bmiddha/shin-ramyun-ai/3D/new_flap.SLDPRT

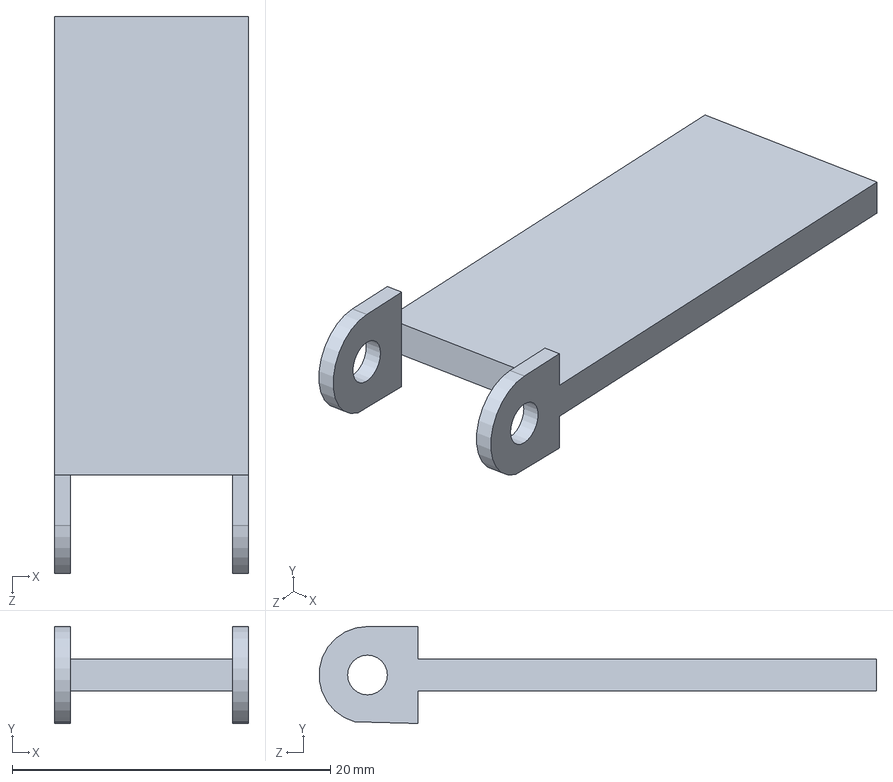
[picture p40: CAD file, 2019-05-07]
3D/new_flap.SLDPRT
12.2 x 6.10 x 35.0 mm
