bmiddha/shin-ramyun-ai/3D/Column Section.SLDPRT

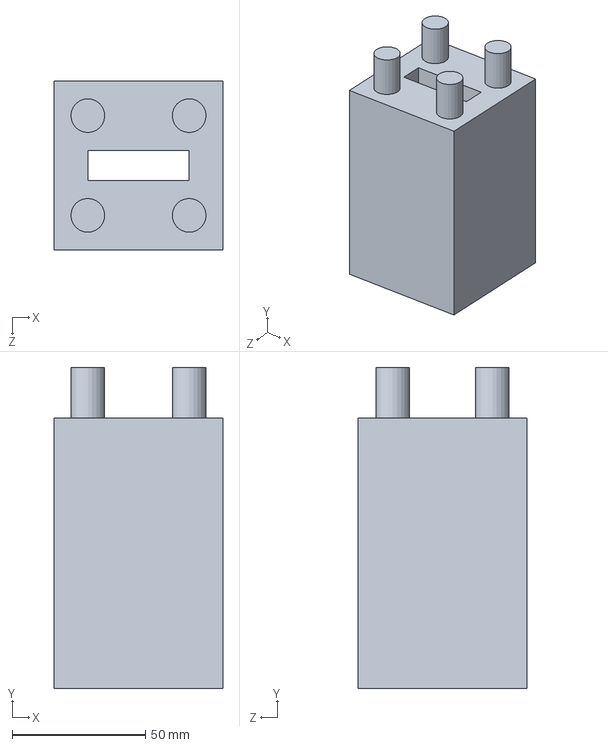
[picture p41: CAD file, 2019-05-07]
3D/Column Section.SLDPRT
63.5 x 120.7 x 63.5 mm
