bmiddha/shin-ramyun-ai/3D/HopperBottom.SLDPRT

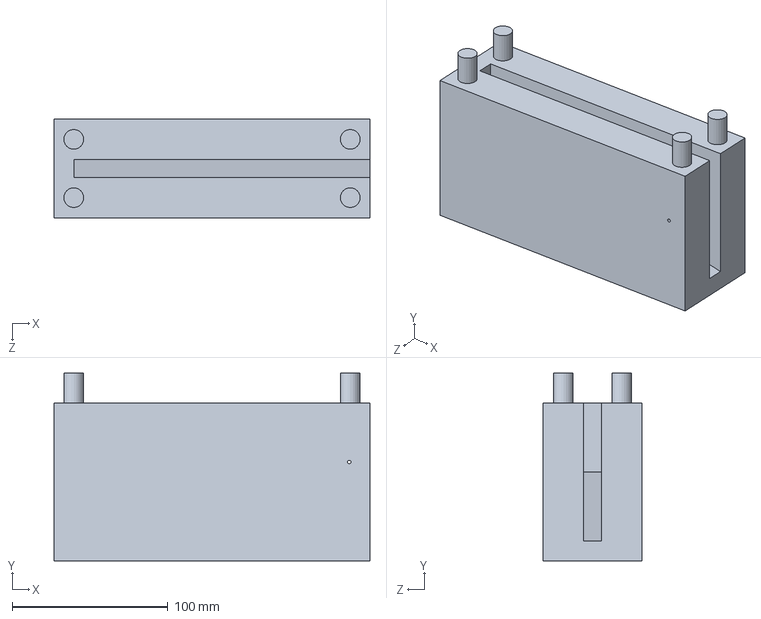
[picture p42: CAD file, 2019-05-07]
3D/HopperBottom.SLDPRT
203.2 x 120.7 x 63.5 mm
