bmiddha/shin-ramyun-ai/3D/Flap_Holder_left.SLDPRT

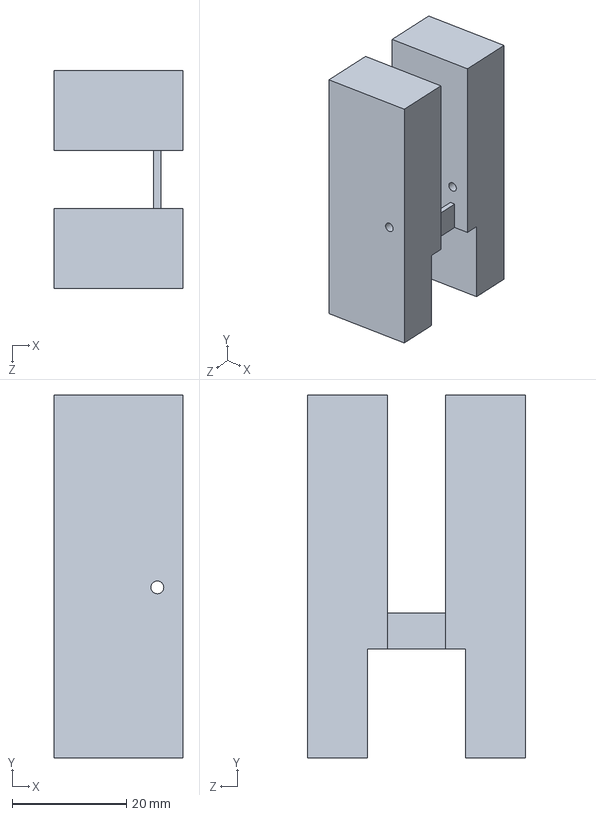
[picture p43: CAD file, 2019-05-07]
3D/Flap_Holder_left.SLDPRT
22.5 x 63.5 x 38.1 mm
