bmiddha/shin-ramyun-ai/3D/column_side.DXF

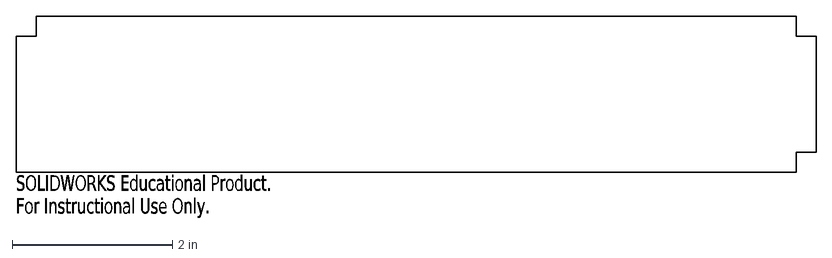
[picture p44: CAD file, 2019-05-07]
3D/column_side.DXF
SOLIDWORKS Educational Product.
For Instructional Use Only.
