bmiddha/shin-ramyun-ai/3D/DispenserRotor.SLDPRT

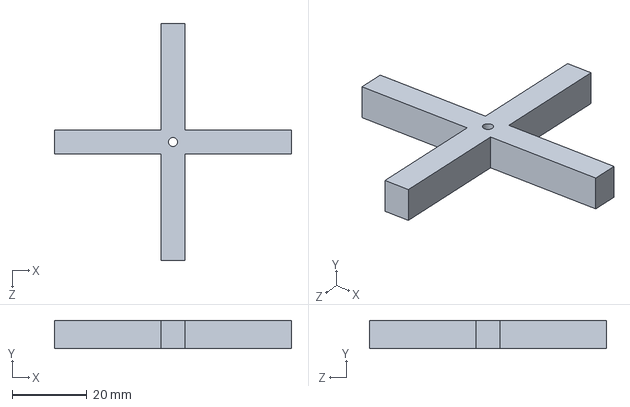
[picture p45: CAD file, 2019-05-07]
3D/DispenserRotor.SLDPRT
63.5 x 7.62 x 63.5 mm
