bmiddha/shin-ramyun-ai/3D/Connect4_Piece.SLDPRT

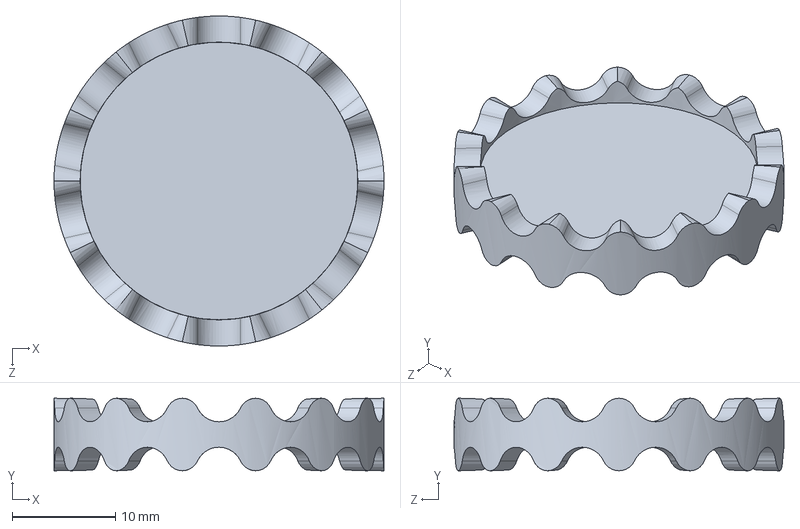
[picture p46: CAD file, 2019-05-07]
3D/Connect4_Piece.SLDPRT
32.0 x 7.04 x 32.0 mm
