bmiddha/shin-ramyun-ai/3D/Flap_Holder.SLDPRT

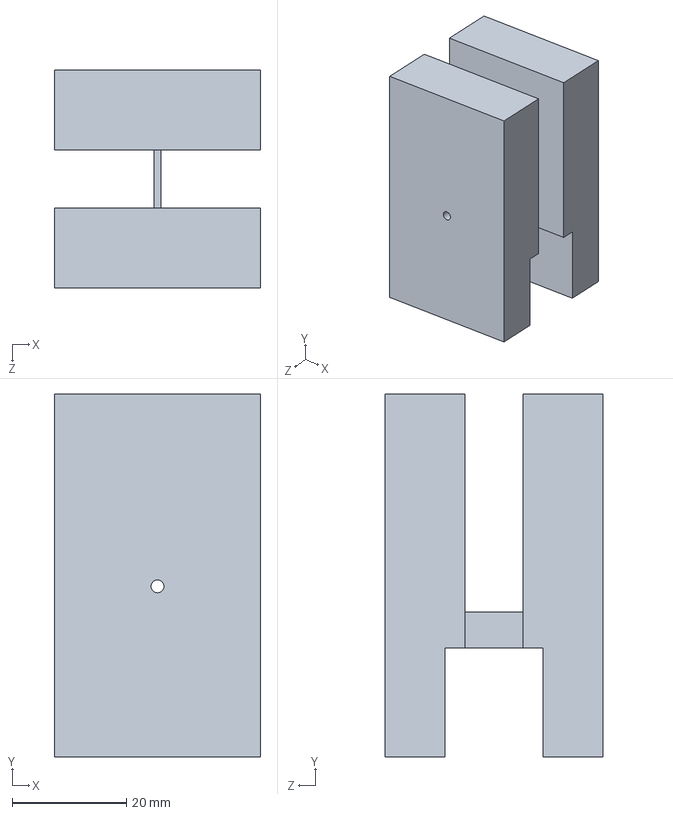
[picture p47: CAD file, 2019-05-07]
3D/Flap_Holder.SLDPRT
36.1 x 63.5 x 38.1 mm
