bmiddha/shin-ramyun-ai/3D/short_i.DXF

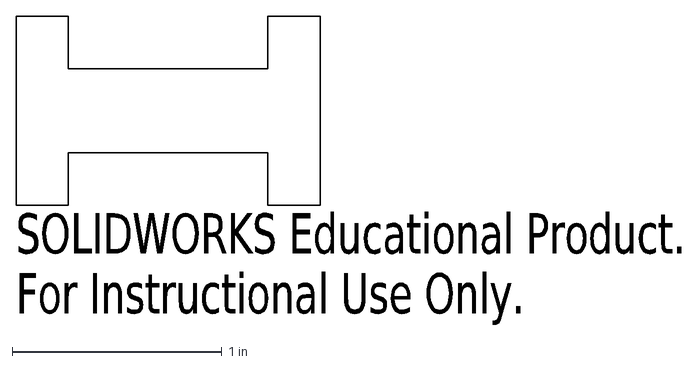
[picture p48: CAD file, 2019-05-07]
3D/short_i.DXF
SOLIDWORKS Educational Product.
For Instructional Use Only.
