bmiddha/shin-ramyun-ai/3D/motor_mount_long.SLDPRT

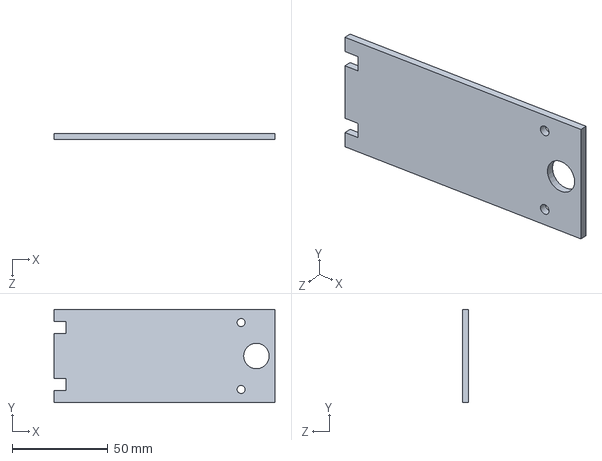
[picture p49: CAD file, 2019-05-07]
3D/motor_mount_long.SLDPRT
115.6 x 48.8 x 3.17 mm
