bmiddha/shin-ramyun-ai/3D/extender_plate.SLDPRT

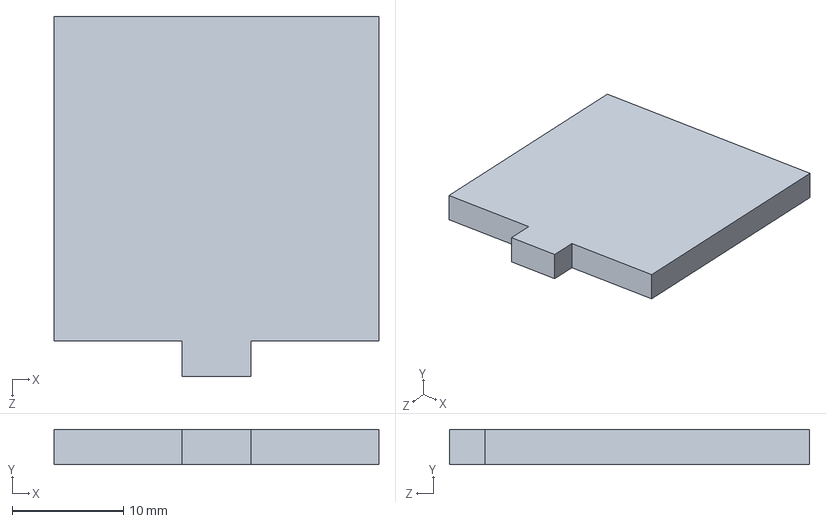
[picture p50: CAD file, 2019-05-07]
3D/extender_plate.SLDPRT
29.2 x 3.17 x 32.4 mm
