bmiddha/shin-ramyun-ai/3D/Connect4_board.SLDPRT

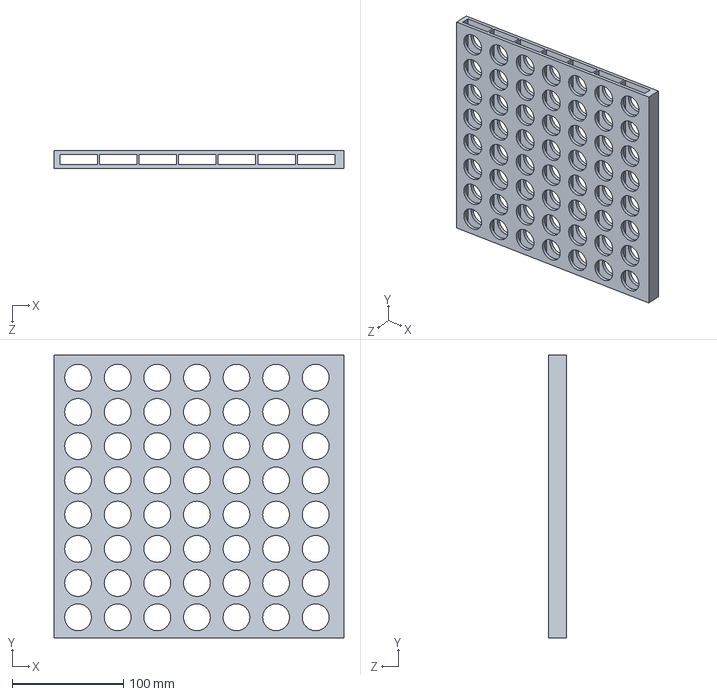
[picture p51: CAD file, 2019-05-07]
3D/Connect4_board.SLDPRT
260.3 x 254.0 x 16.5 mm
