bmiddha/shin-ramyun-ai/3D/2mm_axle.SLDPRT

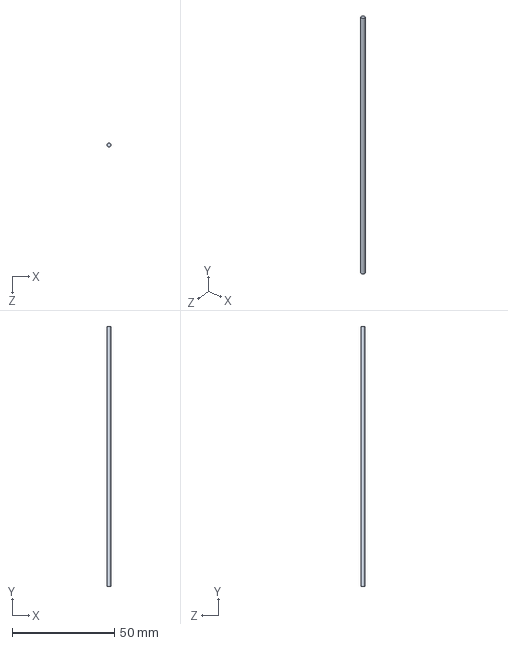
[picture p52: CAD file, 2019-05-07]
3D/2mm_axle.SLDPRT
2.00 x 127.0 x 2.00 mm
