bmiddha/shin-ramyun-ai/3D/Flap_Holder_end.SLDPRT

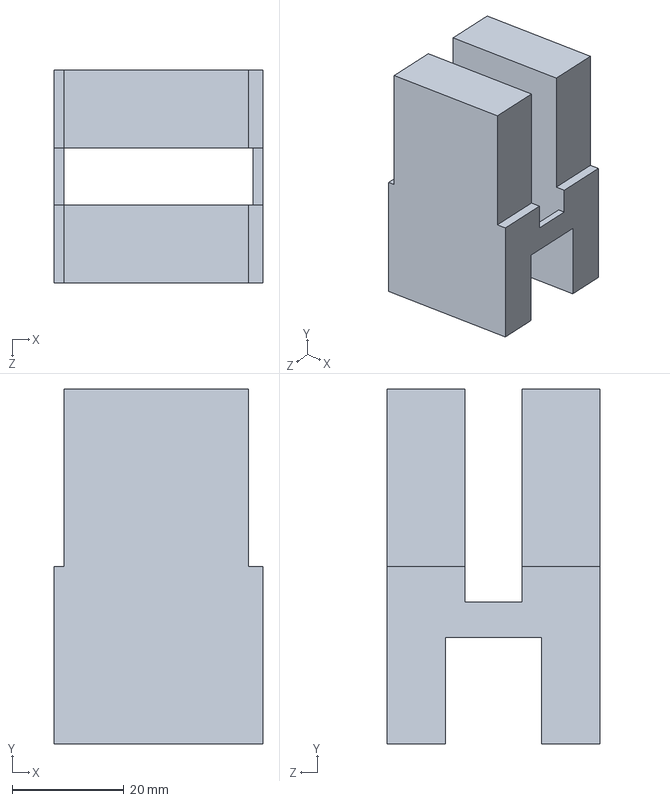
[picture p53: CAD file, 2019-05-07]
3D/Flap_Holder_end.SLDPRT
37.3 x 63.5 x 38.1 mm
