bmiddha/shin-ramyun-ai/3D/track Piece.SLDPRT

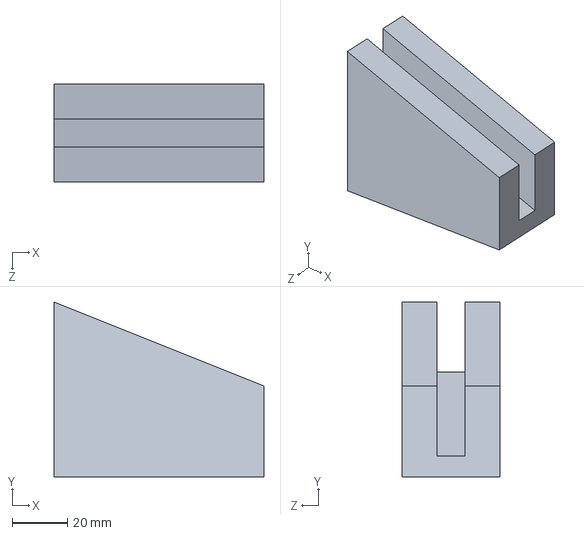
[picture p54: CAD file, 2019-05-07]
3D/track Piece.SLDPRT
76.2 x 63.5 x 35.6 mm
