bmiddha/shin-ramyun-ai/3D/hopper_wall_laser.SLDPRT

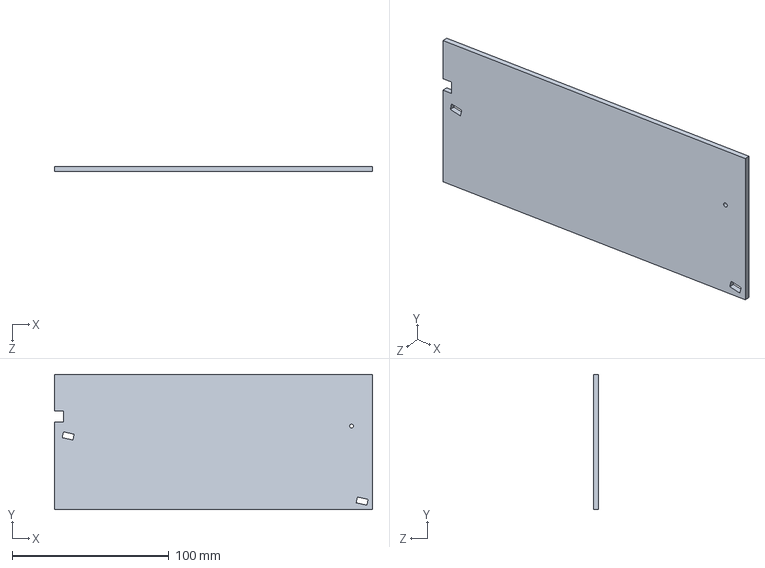
[picture p55: CAD file, 2019-05-07]
3D/hopper_wall_laser.SLDPRT
203.2 x 86.4 x 3.17 mm
