bmiddha/shin-ramyun-ai/3D/axle_holder.DXF

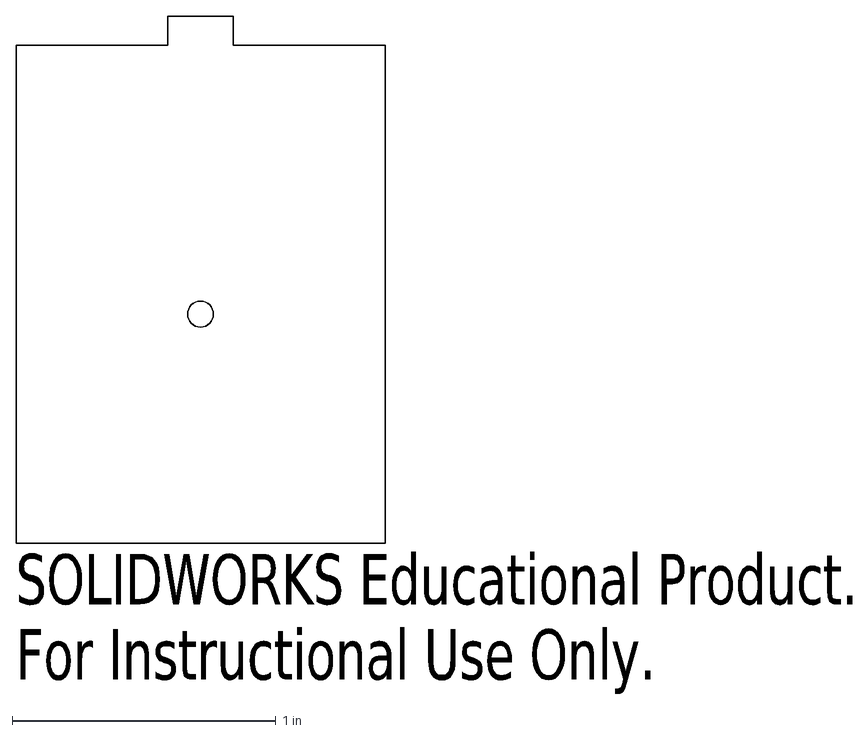
[picture p56: CAD file, 2019-05-07]
3D/axle_holder.DXF
SOLIDWORKS Educational Product.
For Instructional Use Only.
