bmiddha/shin-ramyun-ai/3D/DispenserRotor_larger.DXF

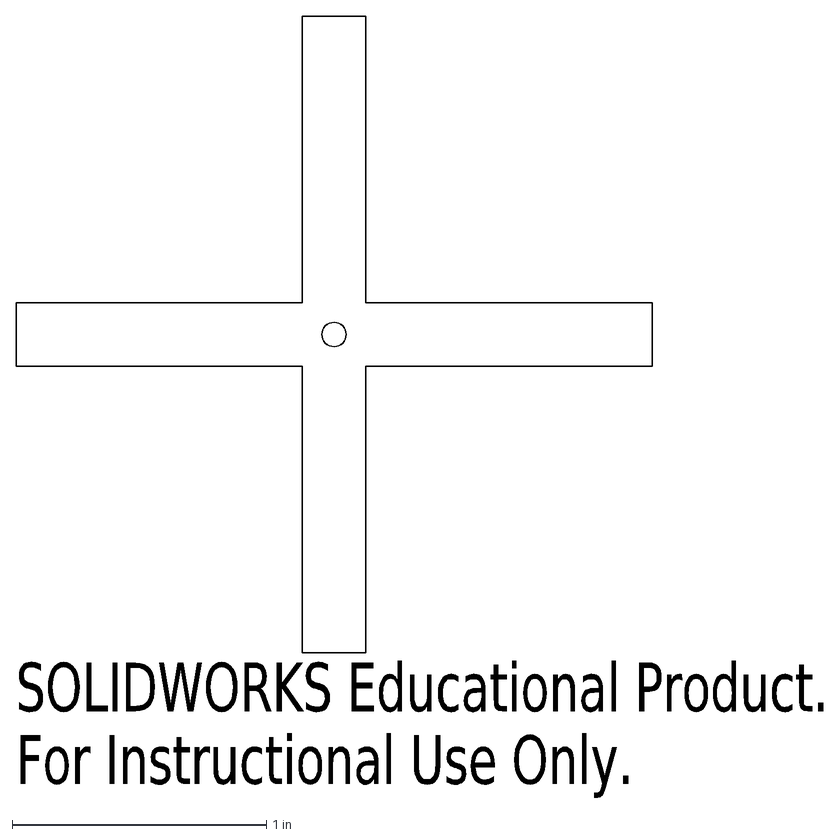
[picture p57: CAD file, 2019-05-07]
3D/DispenserRotor_larger.DXF
SOLIDWORKS Educational Product.
For Instructional Use Only.
