bmiddha/shin-ramyun-ai/3D/motor_mount.SLDPRT

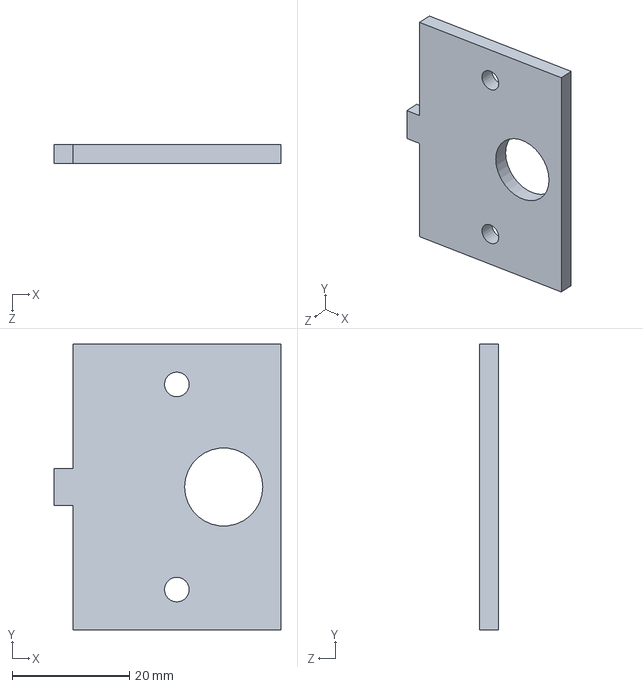
[picture p58: CAD file, 2019-05-07]
3D/motor_mount.SLDPRT
38.6 x 48.8 x 3.17 mm
