bmiddha/shin-ramyun-ai/3D/top_board_face.DXF

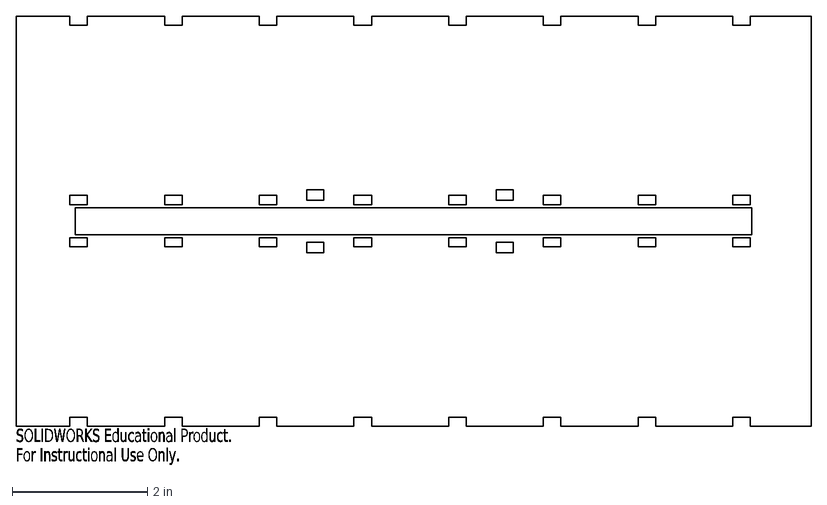
[picture p59: CAD file, 2019-05-07]
3D/top_board_face.DXF
SOLIDWORKS Educational Product.
For Instructional Use Only.
