bmiddha/shin-ramyun-ai/3D/column_laser_side.SLDPRT

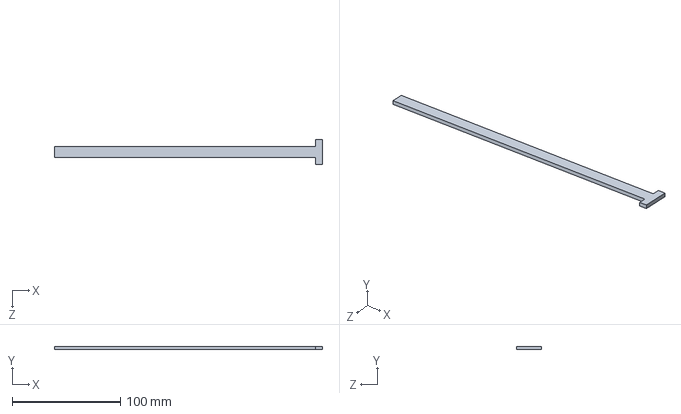
[picture p60: CAD file, 2019-05-07]
3D/column_laser_side.SLDPRT
247.6 x 3.17 x 22.9 mm
