bmiddha/shin-ramyun-ai/3D/Channel_holder.DXF

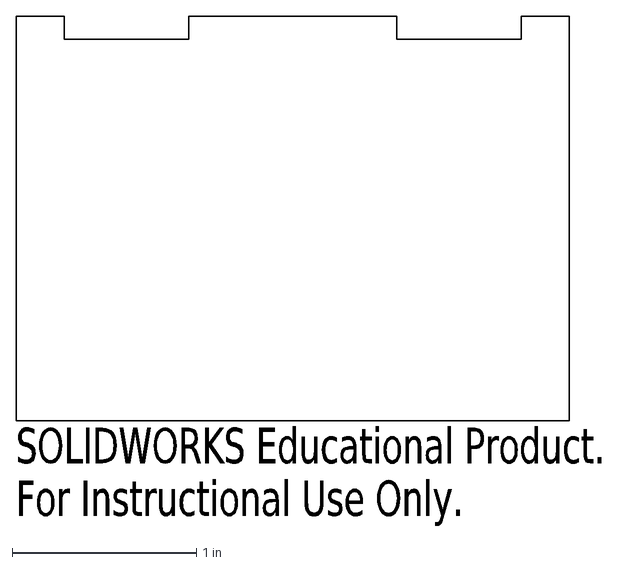
[picture p61: CAD file, 2019-05-07]
3D/Channel_holder.DXF
SOLIDWORKS Educational Product.
For Instructional Use Only.
