bmiddha/shin-ramyun-ai/3D/bottom_aligner.SLDPRT

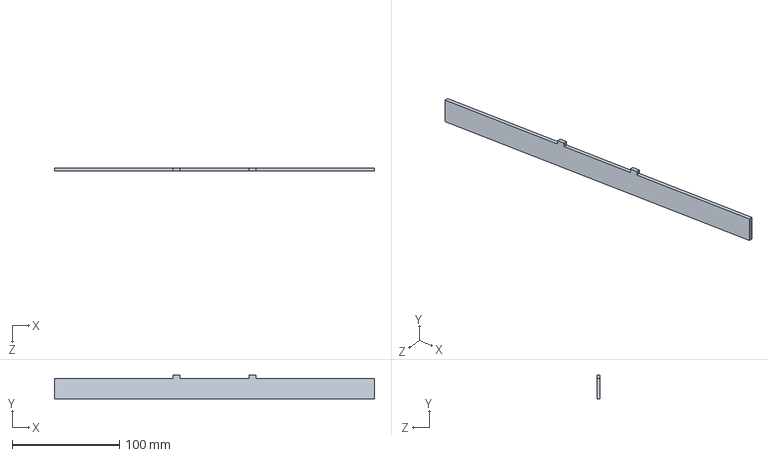
[picture p62: CAD file, 2019-05-07]
3D/bottom_aligner.SLDPRT
298.4 x 22.2 x 3.17 mm
