bmiddha/shin-ramyun-ai/3D/sloped_hopper_piece.SLDPRT

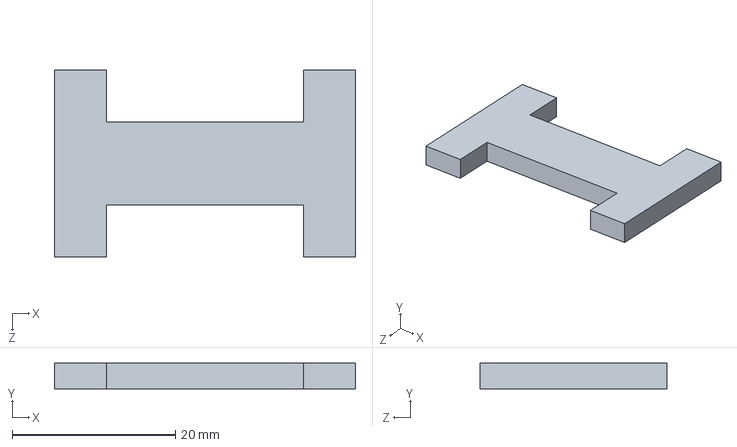
[picture p63: CAD file, 2019-05-07]
3D/sloped_hopper_piece.SLDPRT
36.8 x 3.17 x 22.9 mm
