bmiddha/shin-ramyun-ai/3D/Flap_Holder_leftend.SLDPRT

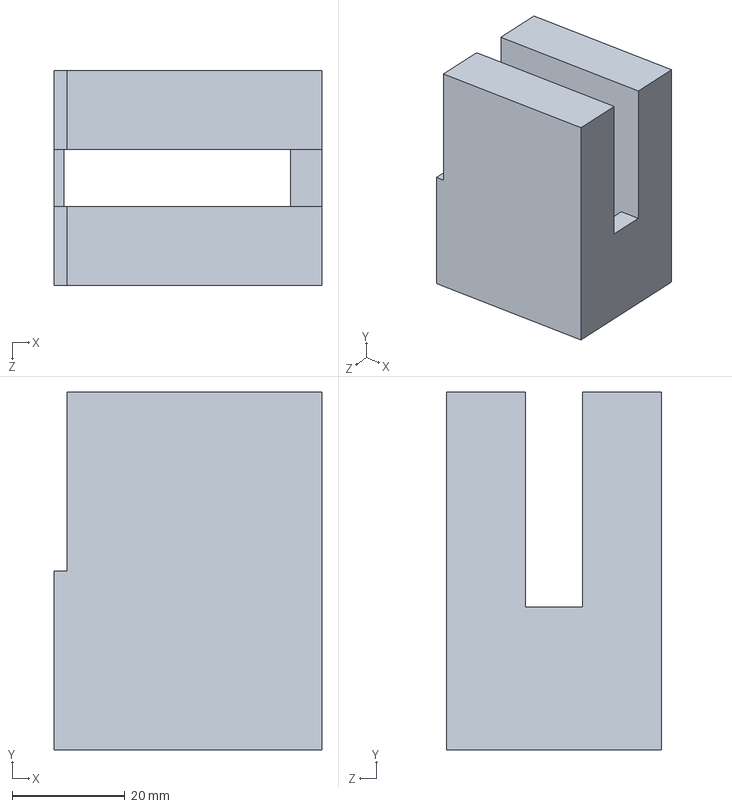
[picture p64: CAD file, 2019-05-07]
3D/Flap_Holder_leftend.SLDPRT
47.5 x 63.5 x 38.1 mm
