bmiddha/shin-ramyun-ai/3D/axe.SLDPRT

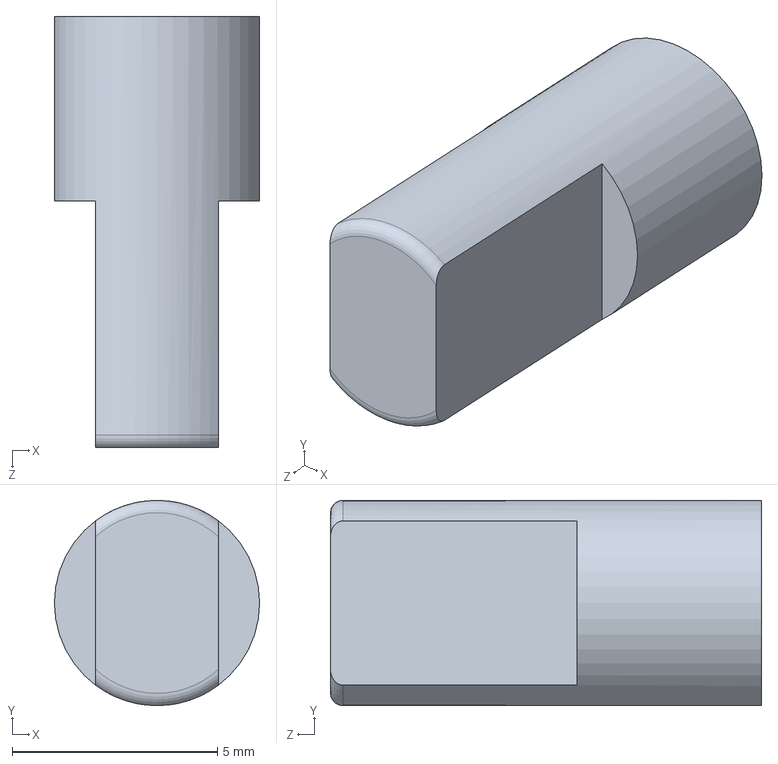
[picture p65: CAD file, 2019-05-07]
3D/axe.SLDPRT
5.00 x 5.00 x 10.5 mm
