bmiddha/shin-ramyun-ai/3D/axle_holder_laser.SLDPRT

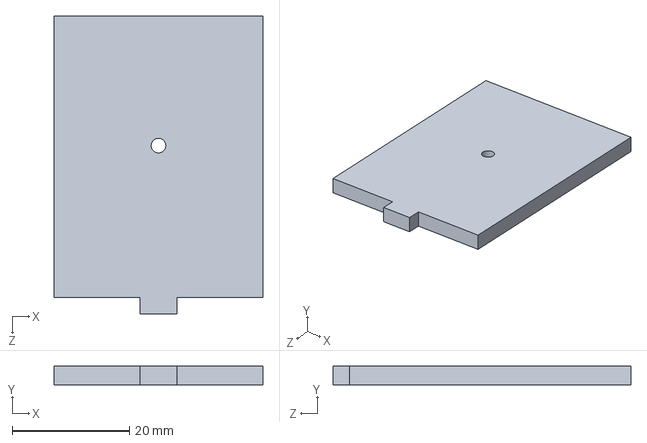
[picture p66: CAD file, 2019-05-07]
3D/axle_holder_laser.SLDPRT
35.6 x 3.17 x 50.8 mm
