bmiddha/shin-ramyun-ai/3D/long_i.DXF

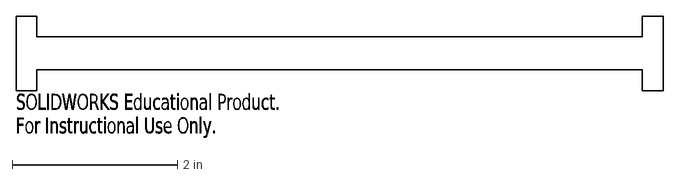
[picture p67: CAD file, 2019-05-07]
3D/long_i.DXF
SOLIDWORKS Educational Product.
For Instructional Use Only.
