bmiddha/shin-ramyun-ai/3D/hopper_wall.DXF

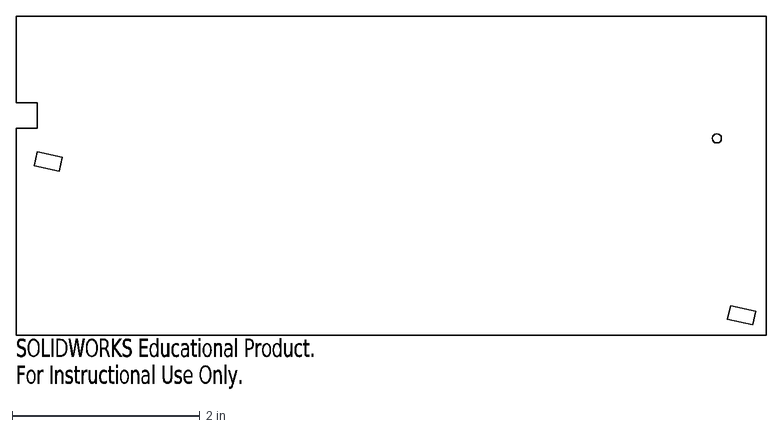
[picture p68: CAD file, 2019-05-07]
3D/hopper_wall.DXF
SOLIDWORKS Educational Product.
For Instructional Use Only.
