bmiddha/shin-ramyun-ai/3D/top_hole_laser.SLDPRT

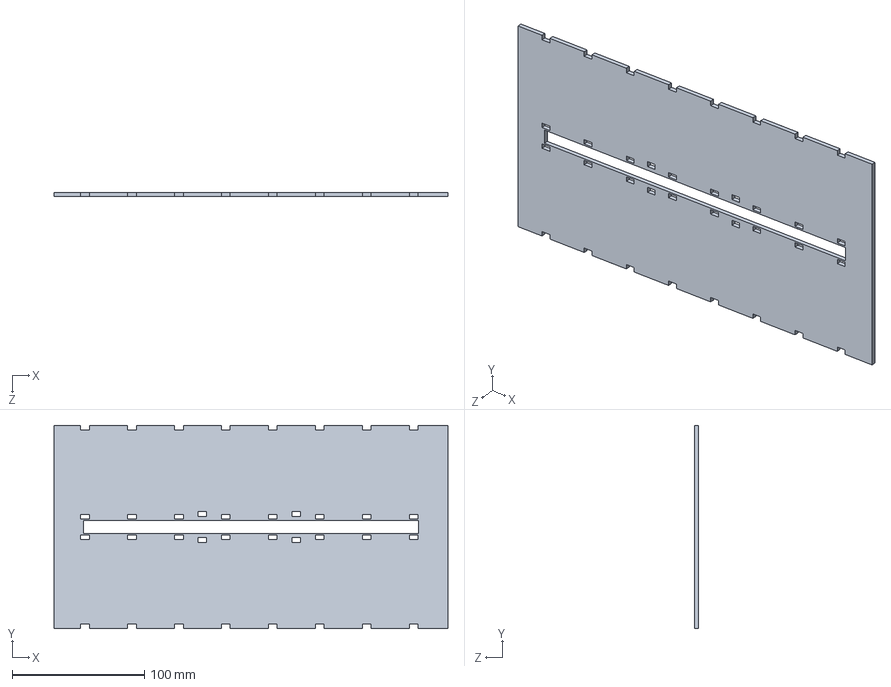
[picture p69: CAD file, 2019-05-07]
3D/top_hole_laser.SLDPRT
298.5 x 153.9 x 3.17 mm
