bmiddha/shin-ramyun-ai/3D/Flap_Holder_rightend.SLDPRT

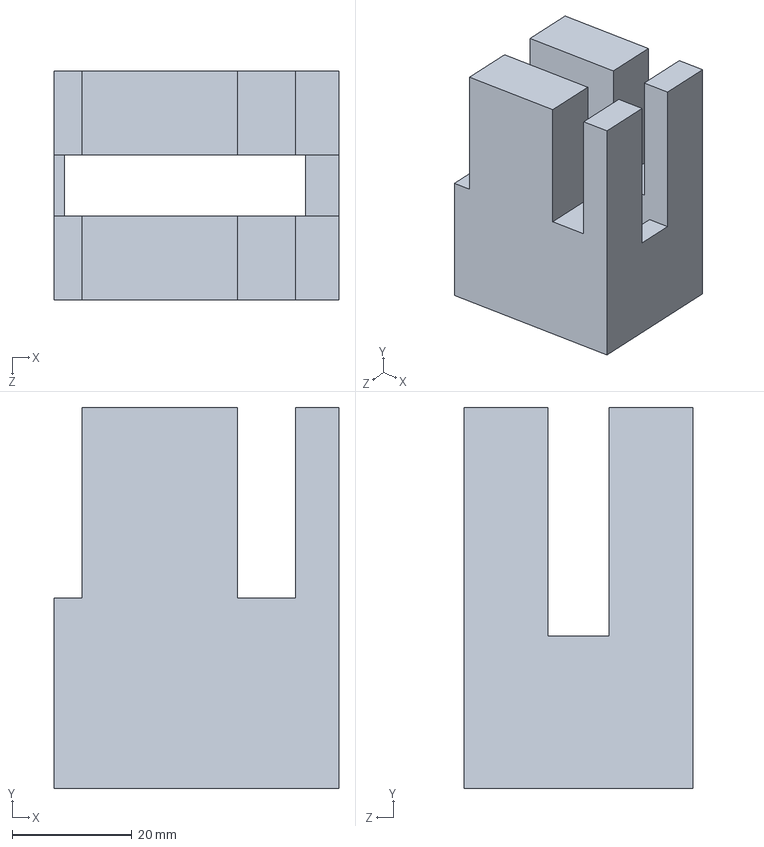
[picture p70: CAD file, 2019-05-07]
3D/Flap_Holder_rightend.SLDPRT
47.5 x 63.5 x 38.1 mm
