bmiddha/shin-ramyun-ai/3D/column_t.DXF

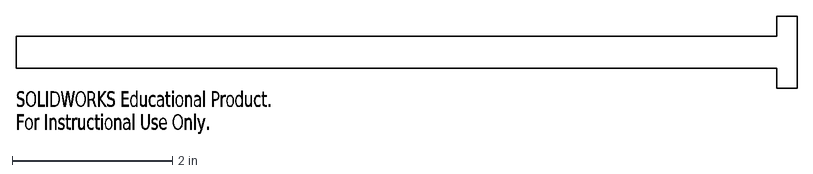
[picture p71: CAD file, 2019-05-07]
3D/column_t.DXF
SOLIDWORKS Educational Product.
For Instructional Use Only.
