bmiddha/shin-ramyun-ai/3D/Channel.SLDPRT

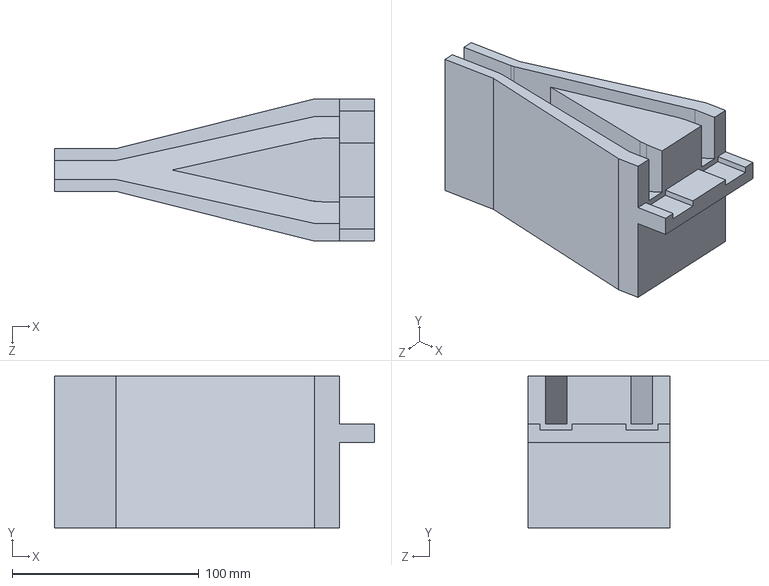
[picture p72: CAD file, 2019-05-07]
3D/Channel.SLDPRT
171.2 x 81.3 x 76.2 mm
