bmiddha/shin-ramyun-ai/3D/cage.SLDPRT

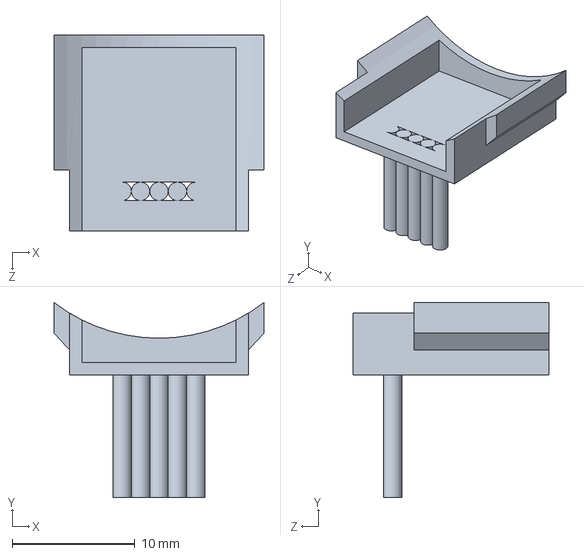
[picture p73: CAD file, 2019-05-07]
3D/cage.SLDPRT
17.1 x 15.9 x 16.0 mm
